DSCodings/Medicin-safe/English/Files/Lazer DXF files/12 top plate LCD.dxf

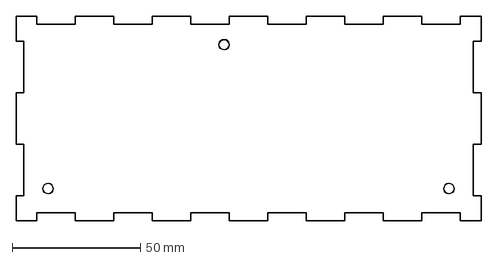
[picture p16: CAD file, 2021-07-01]
English/Files/Lazer DXF files/12 top plate LCD.dxf
181.0 x 79.5 mm
