DSCodings/Medicin-safe/Nederlands/Bestanden/Lazer DXF files/3 binnen dunne cover plaat.dxf

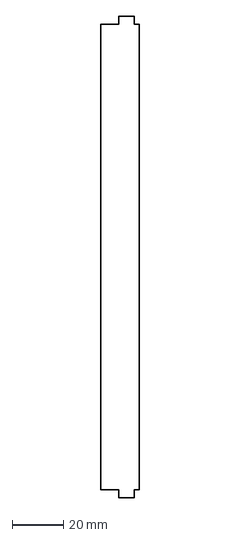
[picture p17: CAD file, 2021-06-25]
Nederlands/Bestanden/Lazer DXF files/3 binnen dunne cover plaat.dxf
15.0 x 187.0 mm
