DSCodings/Medicin-safe/English/Files/3D printer STL files/14 lock pin sleeve large.stl

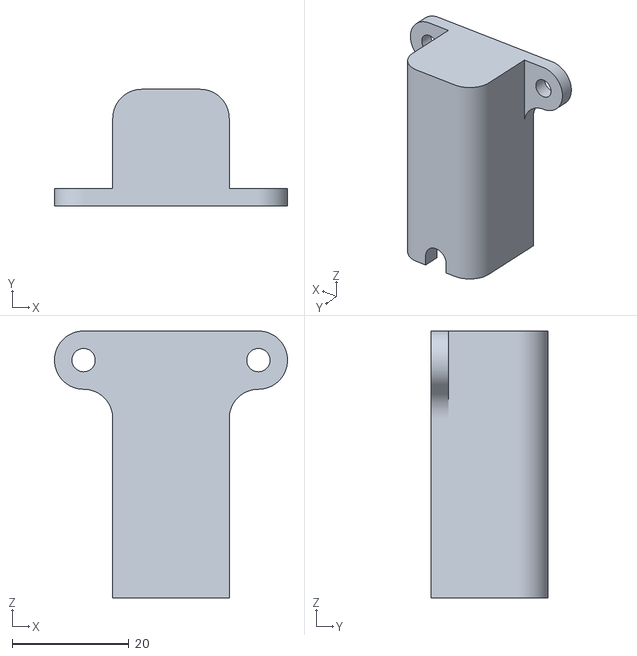
[picture p18: CAD file, 2021-06-25]
English/Files/3D printer STL files/14 lock pin sleeve large.stl
40.0 x 20.0 x 45.8
