DSCodings/Medicin-safe/English/Files/Lazer DXF files/1 inside back plate.dxf

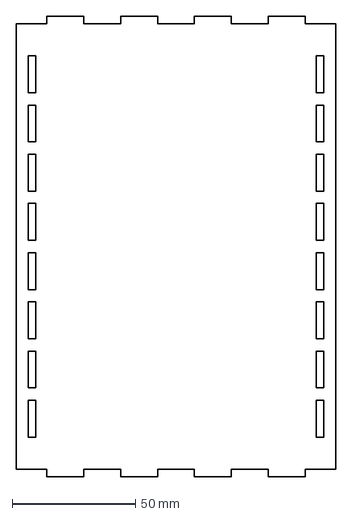
[picture p19: CAD file, 2021-07-01]
English/Files/Lazer DXF files/1 inside back plate.dxf
130.0 x 187.0 mm
