DSCodings/Medicin-safe/Nederlands/Bestanden/Lazer DXF files/20 bakje tussenschot.dxf

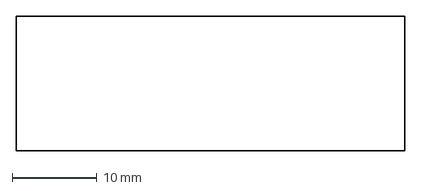
[picture p20: CAD file, 2021-06-25]
Nederlands/Bestanden/Lazer DXF files/20 bakje tussenschot.dxf
45.8 x 15.9 mm
