DSCodings/Medicin-safe/English/Files/3D printer STL files/22 leg mounting corners.stl

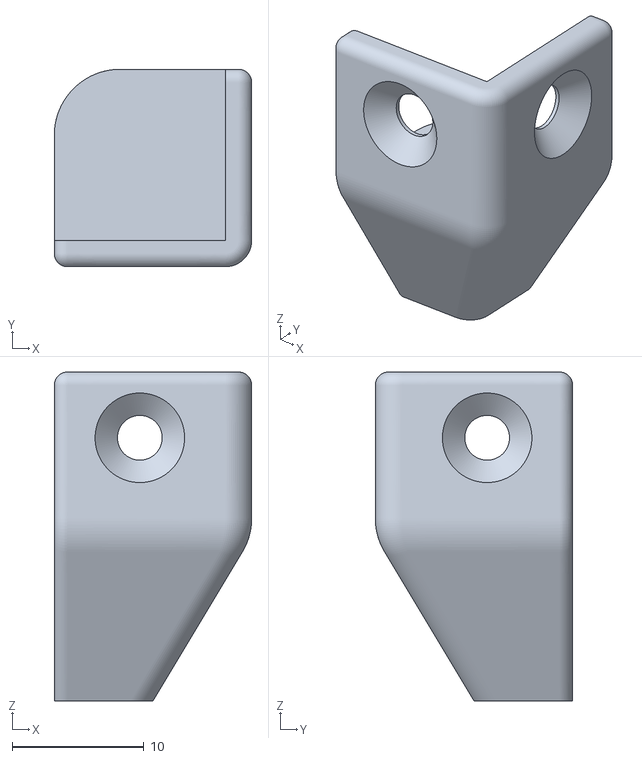
[picture p21: CAD file, 2021-06-25]
English/Files/3D printer STL files/22 leg mounting corners.stl
15.0 x 15.0 x 25.0
