DSCodings/Medicin-safe/English/Files/Lazer DXF files/10 front plate.dxf

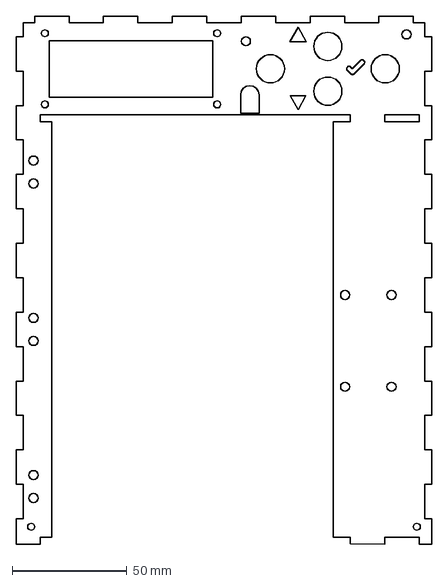
[picture p22: CAD file, 2021-07-01]
English/Files/Lazer DXF files/10 front plate.dxf
181.0 x 230.0 mm
