DSCodings/Medicin-safe/Nederlands/Bestanden/Lazer DXF files/11 deur plaat.dxf

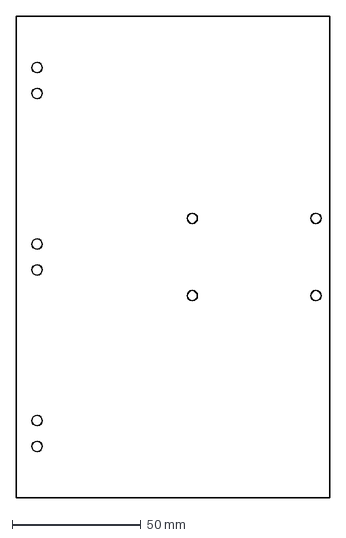
[picture p23: CAD file, 2021-06-25]
Nederlands/Bestanden/Lazer DXF files/11 deur plaat.dxf
121.5 x 187.0 mm
