DSCodings/Medicin-safe/English/Files/3D printer STL files/24 fixing corners 2 sides.stl

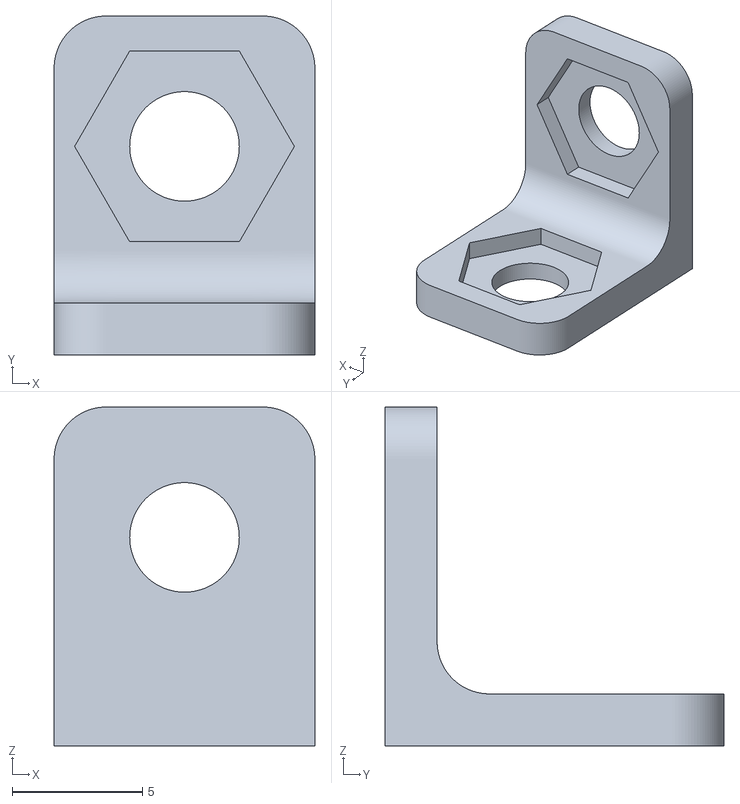
[picture p24: CAD file, 2021-06-25]
English/Files/3D printer STL files/24 fixing corners 2 sides.stl
10.0 x 13.0 x 13.0
