DSCodings/Medicin-safe/English/Files/Lazer DXF files/3 richt cover plate.dxf

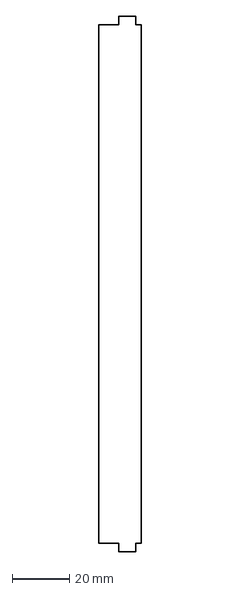
[picture p25: CAD file, 2021-07-01]
English/Files/Lazer DXF files/3 richt cover plate.dxf
15.0 x 187.0 mm
