DSCodings/Medicin-safe/Nederlands/Bestanden/Lazer DXF files/7 achter plaat.dxf

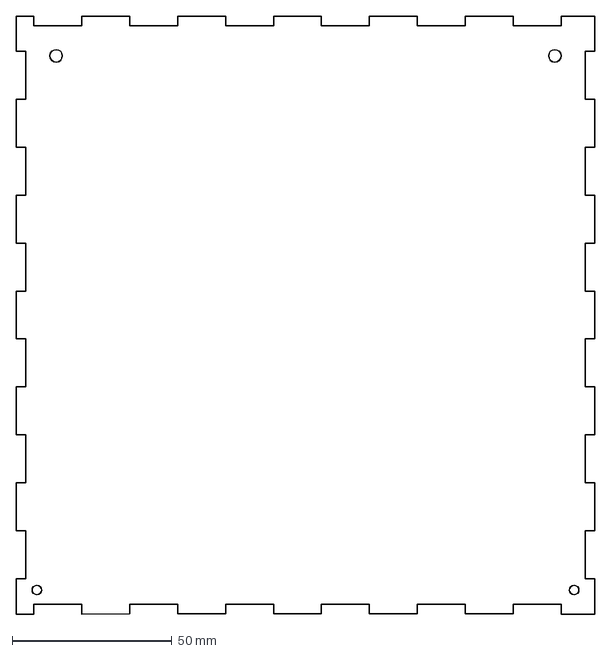
[picture p26: CAD file, 2021-06-25]
Nederlands/Bestanden/Lazer DXF files/7 achter plaat.dxf
181.0 x 187.0 mm
