DSCodings/Medicin-safe/English/Files/Lazer DXF files/9 side plate with RFID.dxf

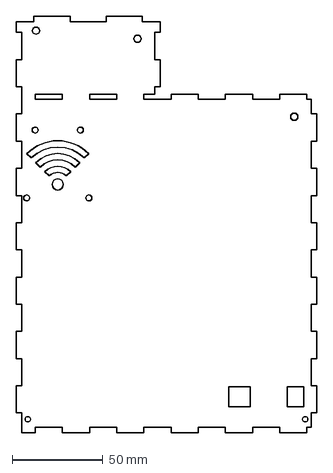
[picture p27: CAD file, 2021-07-01]
English/Files/Lazer DXF files/9 side plate with RFID.dxf
166.0 x 230.0 mm
