DSCodings/Medicin-safe/Nederlands/Bestanden/Lazer DXF files/10.1 lock icon.dxf

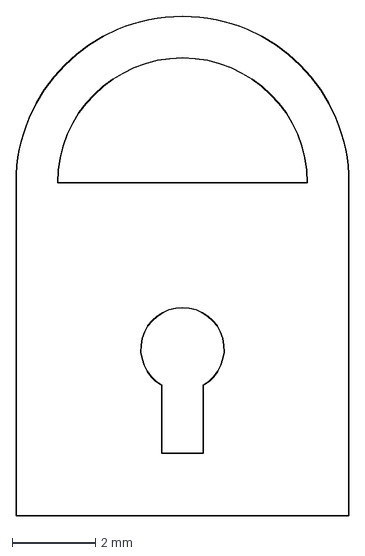
[picture p28: CAD file, 2021-06-25]
Nederlands/Bestanden/Lazer DXF files/10.1 lock icon.dxf
8.00 x 12.0 mm
