DSCodings/Medicin-safe/English/Files/3D printer STL files/23 mounting brackets 3 sides.stl

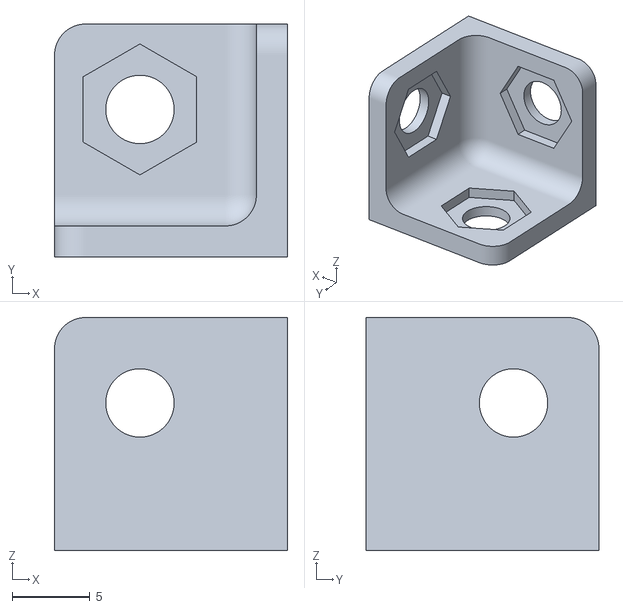
[picture p29: CAD file, 2021-06-25]
English/Files/3D printer STL files/23 mounting brackets 3 sides.stl
15.0 x 15.0 x 15.0
