DSCodings/Medicin-safe/English/Files/Lazer DXF files/6 Top plate.dxf

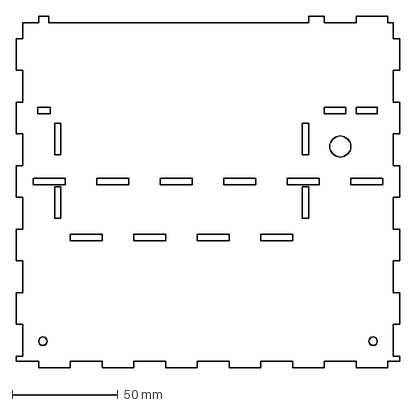
[picture p30: CAD file, 2021-07-01]
English/Files/Lazer DXF files/6 Top plate.dxf
181.0 x 166.0 mm
