DSCodings/Medicin-safe/Nederlands/Bestanden/Lazer DXF files/8 zijplaat.dxf

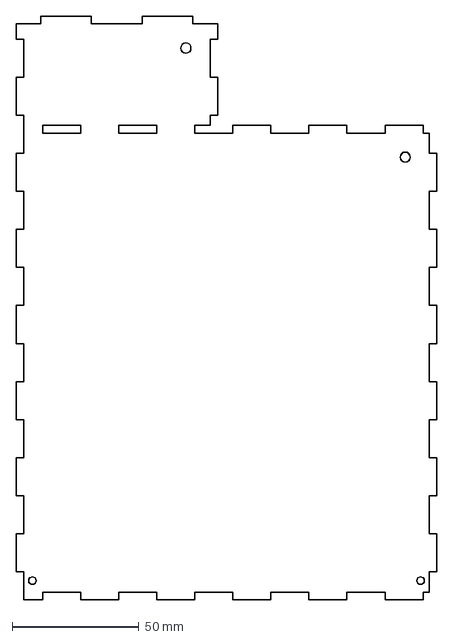
[picture p31: CAD file, 2021-06-25]
Nederlands/Bestanden/Lazer DXF files/8 zijplaat.dxf
166.0 x 230.0 mm
