DSCodings/Medicin-safe/English/Files/3D printer STL files/17 lock counter pin.stl

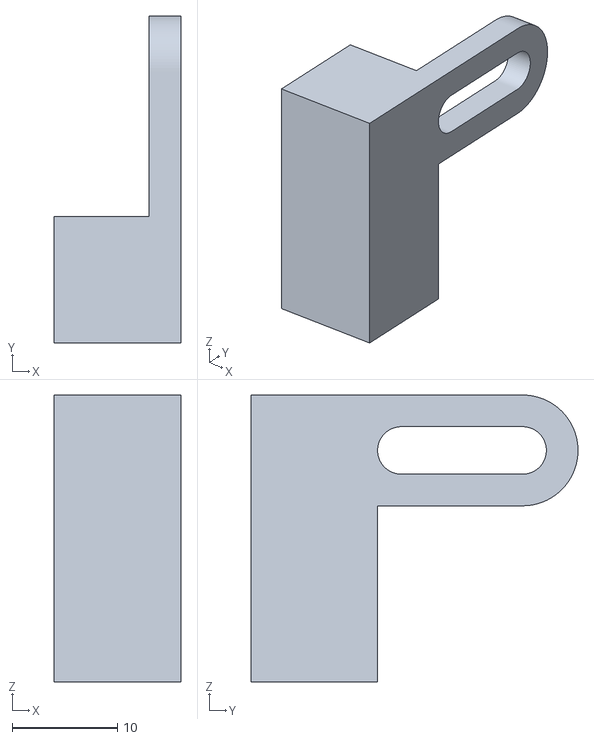
[picture p32: CAD file, 2021-06-25]
English/Files/3D printer STL files/17 lock counter pin.stl
12.0 x 31.0 x 27.2
