DSCodings/Medicin-safe/English/Files/Lazer DXF files/20 tray partition.dxf

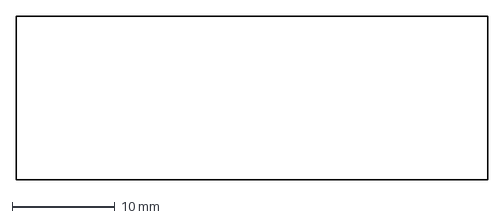
[picture p33: CAD file, 2021-07-01]
English/Files/Lazer DXF files/20 tray partition.dxf
45.8 x 15.9 mm
