DSCodings/Medicin-safe/Nederlands/Bestanden/Lazer DXF files/9 zijplaat met RFID.dxf

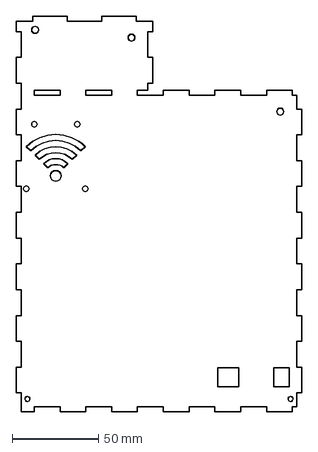
[picture p34: CAD file, 2021-06-25]
Nederlands/Bestanden/Lazer DXF files/9 zijplaat met RFID.dxf
166.0 x 230.0 mm
