DSCodings/Medicin-safe/English/Files/3D printer STL files/15 lock pin sleeve smal.stl

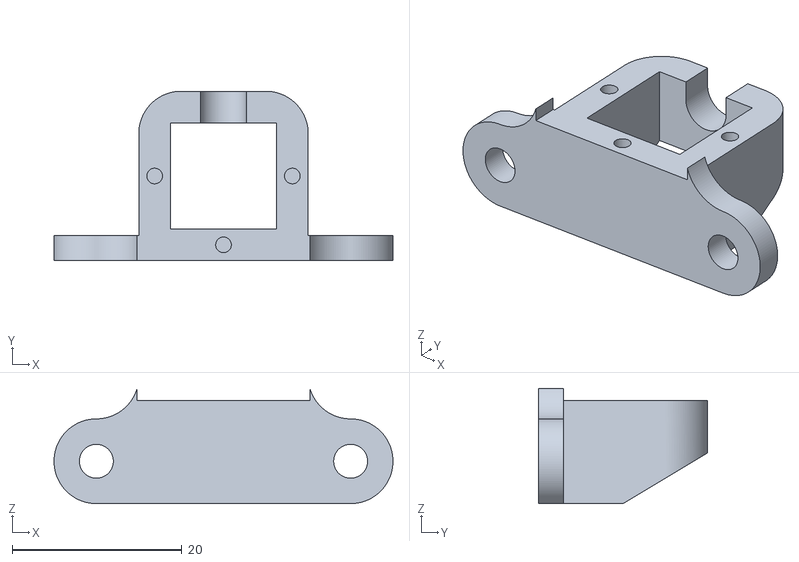
[picture p35: CAD file, 2021-06-25]
English/Files/3D printer STL files/15 lock pin sleeve smal.stl
40.0 x 20.0 x 13.6
