DSCodings/Medicin-safe/English/Files/Lazer DXF files/8 side plate.dxf

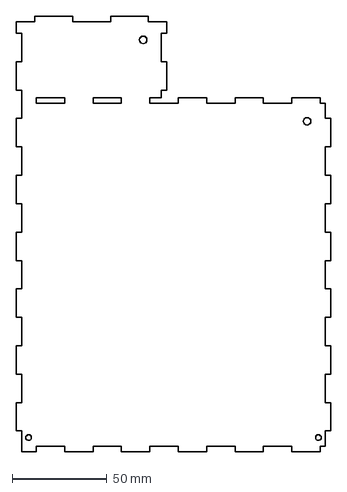
[picture p36: CAD file, 2021-07-01]
English/Files/Lazer DXF files/8 side plate.dxf
166.0 x 230.0 mm
