DSCodings/Medicin-safe/Nederlands/Bestanden/Lazer DXF files/10 voor plaat.dxf

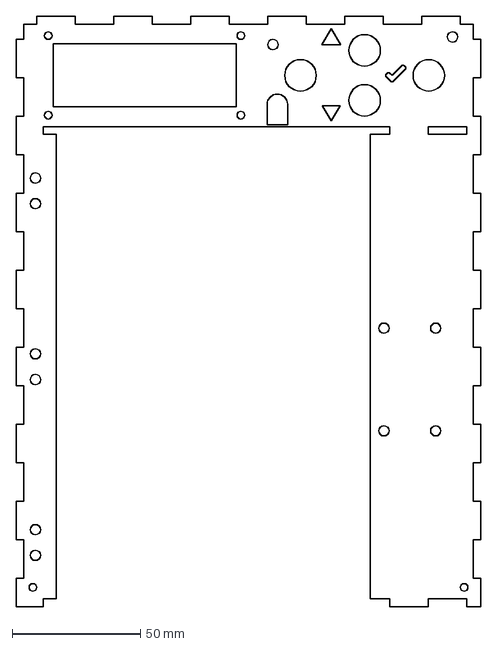
[picture p37: CAD file, 2021-06-25]
Nederlands/Bestanden/Lazer DXF files/10 voor plaat.dxf
181.0 x 230.0 mm
