DSCodings/Medicin-safe/English/Files/3D printer STL files/18 pin shooter.stl

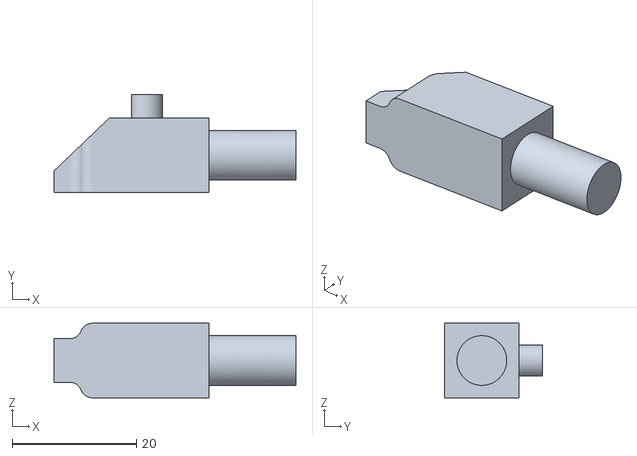
[picture p38: CAD file, 2021-06-25]
English/Files/3D printer STL files/18 pin shooter.stl
38.9 x 15.8 x 12.0
