DSCodings/Medicin-safe/English/Files/Lazer DXF files/11 door plate.dxf

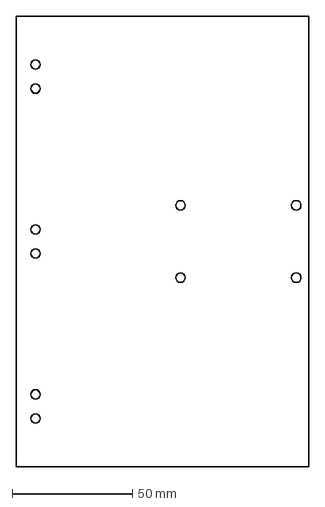
[picture p39: CAD file, 2021-07-01]
English/Files/Lazer DXF files/11 door plate.dxf
121.5 x 187.0 mm
