DSCodings/Medicin-safe/Nederlands/Bestanden/Lazer DXF files/6 boven plaat.dxf

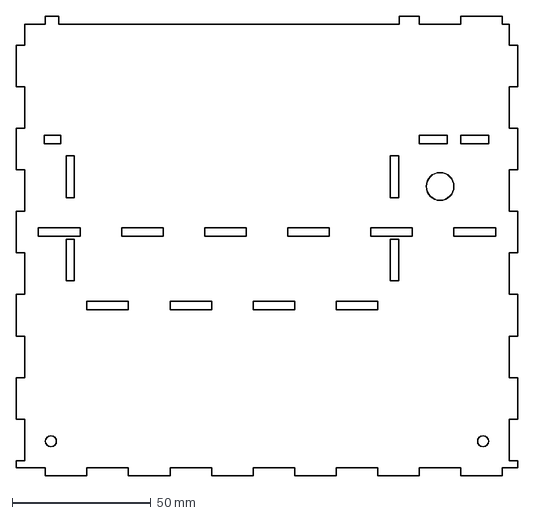
[picture p40: CAD file, 2021-06-25]
Nederlands/Bestanden/Lazer DXF files/6 boven plaat.dxf
181.0 x 166.0 mm
