DSCodings/Medicin-safe/English/Files/3D printer STL files/19 tray shelf.stl

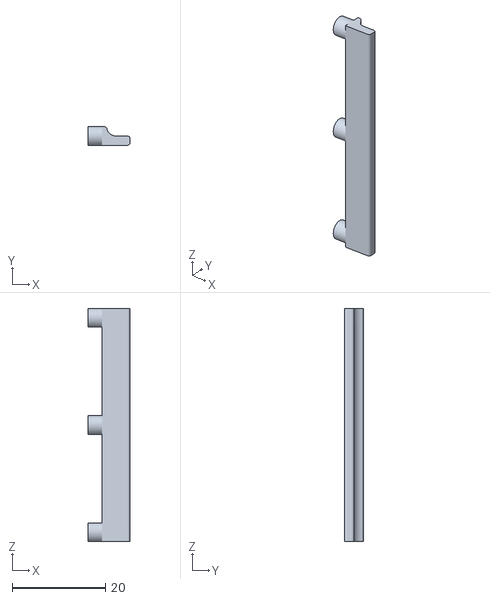
[picture p41: CAD file, 2021-06-25]
English/Files/3D printer STL files/19 tray shelf.stl
9.00 x 4.00 x 50.0
