DSCodings/Medicin-safe/English/Files/Lazer DXF files/4 left cover plate.dxf

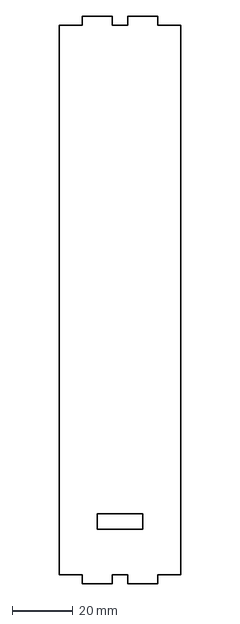
[picture p42: CAD file, 2021-07-01]
English/Files/Lazer DXF files/4 left cover plate.dxf
40.0 x 187.0 mm
