DSCodings/Medicin-safe/Nederlands/Bestanden/Lazer DXF files/13 achter plaat LCD.dxf

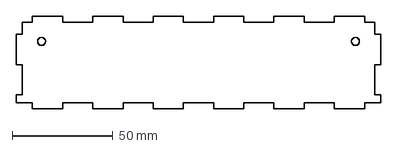
[picture p43: CAD file, 2021-06-25]
Nederlands/Bestanden/Lazer DXF files/13 achter plaat LCD.dxf
181.0 x 46.0 mm
