DSCodings/Medicin-safe/English/Files/Lazer DXF files/5 bottom plate.dxf

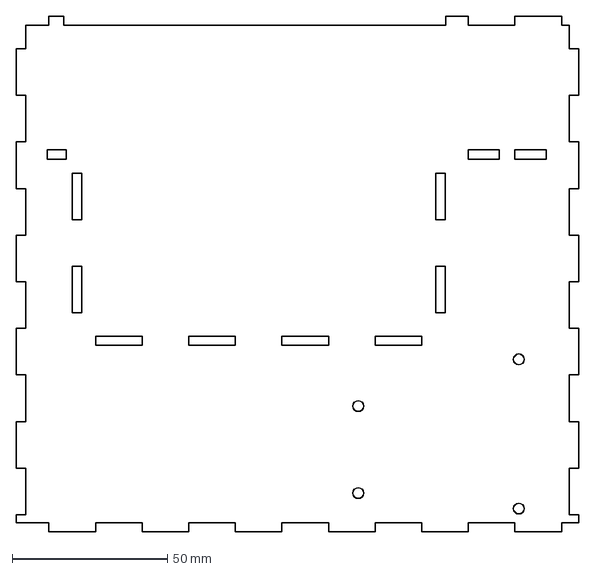
[picture p44: CAD file, 2021-07-01]
English/Files/Lazer DXF files/5 bottom plate.dxf
181.0 x 166.0 mm
