DSCodings/Medicin-safe/Nederlands/Bestanden/Lazer DXF files/4 binnen dikke cover plaat.dxf

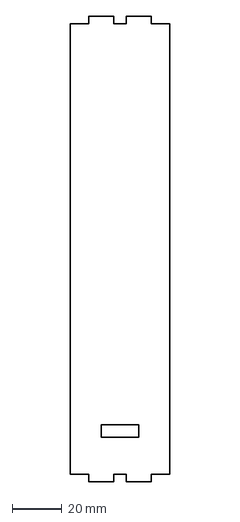
[picture p45: CAD file, 2021-06-25]
Nederlands/Bestanden/Lazer DXF files/4 binnen dikke cover plaat.dxf
40.0 x 187.0 mm
