DSCodings/Medicin-safe/Nederlands/Bestanden/Lazer DXF files/2 binnen zijplaat.dxf

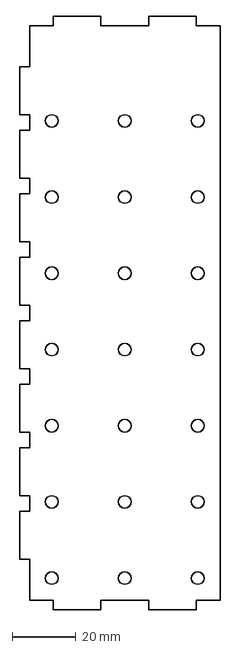
[picture p46: CAD file, 2021-06-25]
Nederlands/Bestanden/Lazer DXF files/2 binnen zijplaat.dxf
63.0 x 187.0 mm
